DylanCoon99/auto_tracking_gimbal/images/31870361_2032062476807216_3422363605130018816_n.jpg

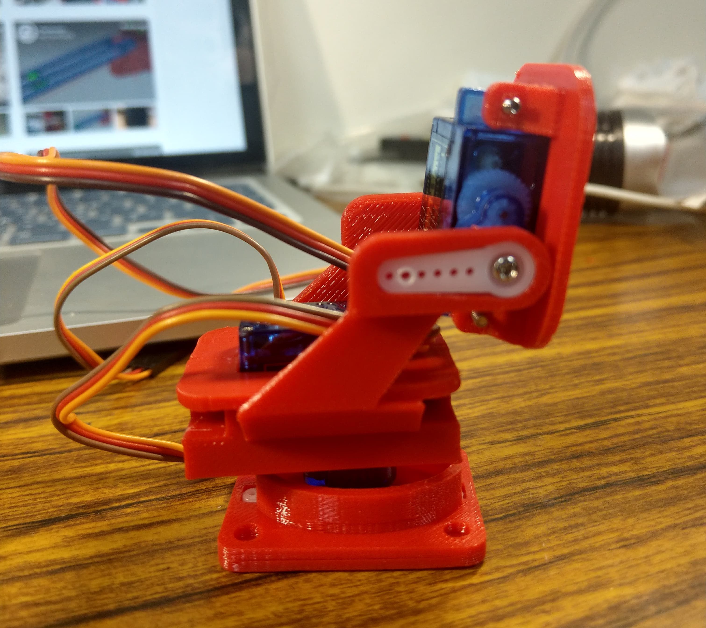
images/31870361_2032062476807216_3422363605130018816_n.jpg
