DylanCoon99/auto_tracking_gimbal/images/31900915_2032062416807222_4156219726122450944_n.jpg

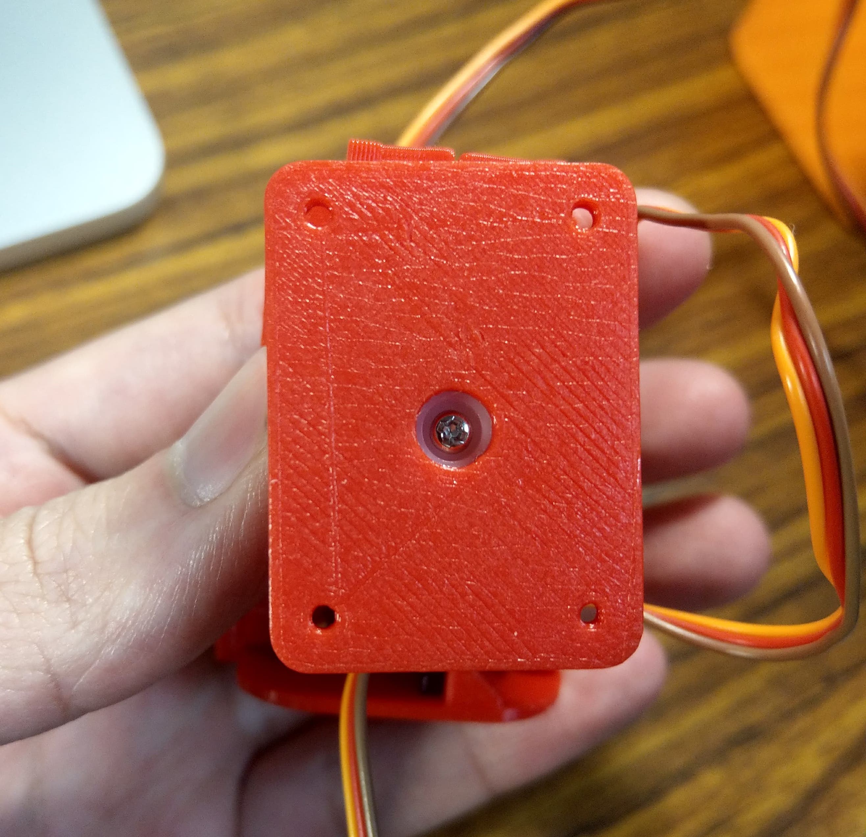
images/31900915_2032062416807222_4156219726122450944_n.jpg
